kaelhem/memoprout/memoprout-arduino/MemoProut_calibration.h

/*
  CalibrationUtils.h - Library that helps to save and load data in EEPROM.
  Created by klem on 17/05/2019
*/
#ifndef CalibrationUtils_h
#define CalibrationUtils_h

#include "Arduino.h"
#include <EEPROM.h>
#include "MemoProut_ledButton.h"

struct CalibrationObject {
  unsigned long memoryId;
  int buttons[14];
};

class CalibrationUtils
{
  public:
    CalibrationUtils();
    static bool isCalibrated();
    static CalibrationObject loadCalibration();
    static void saveCalibration(int buttons[14]);
};

#endif
